jeffmhopkins/Open-Woodwind-Project/src/owp_synth/patches.ino

/*
 * The Open Woodwind Project - OWP_Synth for Woodwind Controllers by Jeff Hopkins
 * 
 * =============================================================================================================================================
 * 
 * Handles saving and loading the patch files from the SD card and EEPROM, defines the CC numbers
 * 
 */
 
#include <EEPROM.h>

#define CC_MODULATION_WHEEL               1
#define CC_BREATH                         2
#define CC_EXPRESSION                     11
#define CC_BREATH_TO_PULSE_WIDTH          20
#define CC_BREATH_TO_FILTER_CUTOFF        21
#define CC_BREATH_TO_FILTER_RESONANCE     22
#define CC_BREATH_TO_OVERDRIVE            23
#define CC_MODULATION_TO_PULSE_WIDTH      24
#define CC_MODULATION_TO_FILTER_CUTOFF    25
#define CC_MODULATION_TO_FILTER_RESONANCE 26
#define CC_MODULATION_TO_OVERDRIVE        27
#define CC_EXPRESSION_TO_PULSE_WIDTH      28
#define CC_EXPRESSION_TO_FILTER_CUTOFF    29
#define CC_EXPRESSION_TO_FILTER_RESONANCE 30
#define CC_EXPRESSION_TO_PORTAMENTO       31
#define CC_EXPRESSION_TO_OVERDRIVE        32
#define CC_PORTAMENTO_MIN_MULTIPLIER      33
#define CC_WAV_PLAYER                     34
#define CC_WAV_PLAYER_GAIN                35
#define CC_LOAD_PATCH                     36
#define CC_SAVE_PATCH                     37
#define CC_LFO1_FREQUENCY                 38
#define CC_LFO1_AMOUNT                    39
#define CC_LFO1_RANGE                     40
#define CC_WAVE1_SHAPE                    41
#define CC_WAVE2_SHAPE                    42
#define CC_WAVE3_SHAPE                    43
#define CC_WAVE4_SHAPE                    44
#define CC_LFO2_FREQUENCY                 45
#define CC_LFO2_AMOUNT                    46
#define CC_LFO2_RANGE                     47
#define CC_MODULATION_TO_LFO1_GAIN        48
#define CC_BREATH_TO_LFO1_GAIN            49
#define CC_EXPRESSION_TO_LFO1_GAIN        50
#define CC_WAVE1_GAIN                     51
#define CC_WAVE2_GAIN                     52
#define CC_WAVE3_GAIN                     53
#define CC_WAVE4_GAIN                     54
#define CC_MODULATION_TO_LFO1_FREQ        55
#define CC_BREATH_TO_LFO1_FREQ            56
#define CC_EXPRESSION_TO_LFO1_FREQ        57
#define CC_MODULATION_TO_LFO2_GAIN        58
#define CC_BREATH_TO_LFO2_GAIN            59
#define CC_EXPRESSION_TO_LFO2_GAIN        60
#define CC_WAVE1_DETUNE_MULTIPLIER        61
#define CC_WAVE2_DETUNE_MULTIPLIER        62
#define CC_WAVE3_DETUNE_MULTIPLIER        63
#define CC_WAVE4_DETUNE_MULTIPLIER        64
#define CC_MODULATION_TO_LFO2_FREQ        65
#define CC_BREATH_TO_LFO2_FREQ            66
#define CC_EXPRESSION_TO_LFO2_FREQ        67
#define CC_MODULATION_TO_LFO1_RANGE       68
#define CC_BREATH_TO_LFO1_RANGE           69
#define CC_EXPRESSION_TO_LFO1_RANGE       70
#define CC_WAVE1_PULSE_WIDTH              71
#define CC_WAVE2_PULSE_WIDTH              72
#define CC_WAVE3_PULSE_WIDTH              73
#define CC_WAVE4_PULSE_WIDTH              74
#define CC_FILTER_RESONANCE_OFFSET        76
#define CC_NOTE_OFFSET                    77
#define CC_FINE_TUNING                    78
#define CC_MASTER_VOLUME                  81
#define CC_FILTER_FREQUENCY_OFFSET        82
#define CC_NOISE_PINK_GAIN                83
#define CC_NOISE_WHITE_GAIN               84
#define CC_EFFECTS_MIXER_CLEAN            85
#define CC_EFFECTS_MIXER_FLANGE           86
#define CC_EFFECTS_MIXER_CHORUS           87
#define CC_EFFECTS_MIXER_DELAY            90
#define CC_REVERB_ROOM_SIZE               91
#define CC_EFFECTS_MIXER_DELAY_MS         92
#define CC_MODULATION_TO_LFO2_RANGE       93
#define CC_BREATH_TO_LFO2_RANGE           94
#define CC_EXPRESSION_TO_LFO2_RANGE       95
#define CC_WAVESHAPE1_GAIN                96
#define CC_WAVESHAPE2_GAIN                97
#define CC_WAVESHAPE3_GAIN                98
#define CC_WAVESHAPE4_GAIN                99
#define CC_WAVESHAPE_MODULATION_MULTIPLIER        100
#define CC_WAVESHAPE_MODULATION_MULTIPLIER_OFFSET 101
#define CC_WAVESHAPE_CLEAN_GAIN                   102
#define CC_LFO1_DESTINATION_FREQUENCY     103
#define CC_LFO1_DESTINATION_GAIN          104
#define CC_LFO1_DESTINATION_FILTER        105
#define CC_LFO2_DESTINATION_FREQUENCY     106
#define CC_LFO2_DESTINATION_GAIN          107
#define CC_LFO2_DESTINATION_FILTER        108
#define CC_LFO_RESET_PHASE_ON_NEW_NOTE    109
#define CC_BREATH_TO_WAVE2_WAVE3_WAVE4_GAIN     110
#define CC_MODULATION_TO_WAVE2_WAVE3_WAVE4_GAIN 111
#define CC_EXPRESSION_TO_WAVE2_WAVE3_WAVE4_GAIN 112
#define CC_WAVE2_WAVE3_WAVE4_GAIN_MODULATION_OFFSET   113 
#define CC_VCA_GATE_BYPASS                114
#define CC_FILTER_BYPASS                  115
#define CC_FILTER_TYPE                    116
#define CC_AUDIO_IN_PRE                   117
#define CC_AUDIO_IN_POST                  118
#define CC_EQ_1                           12
#define CC_EQ_2                           13
#define CC_EQ_3                           14
#define CC_EQ_4                           15
#define CC_EQ_5                           16
#define CC_BREATH_GAMMA                   17
#define CC_REVERB_WET                     18

struct Patch {
  float wave1_shape, wave2_shape, wave3_shape, wave4_shape;
  float wave1_pulse_width, wave2_pulse_width, wave3_pulse_width, wave4_pulse_width;
  float wave1_detune_multiplier, wave2_detune_multiplier, wave3_detune_multiplier, wave4_detune_multiplier;
  float wave1_gain,  wave2_gain,  wave3_gain,  wave4_gain;
  float master_volume, reverb_size;
  float noise_pink_gain, noise_white_gain;
  float filter_min_frequency, filter_q;
  float breath_to_pulse_width, breath_to_filter_cutoff, breath_to_filter_resonance, breath_to_overdrive;
  float modulation_to_pulse_width, modulation_to_filter_cutoff, modulation_to_filter_resonance, modulation_to_overdrive;
  float expression_to_pulse_width, expression_to_filter_cutoff, expression_to_filter_resonance, expression_to_portamento, expression_to_overdrive;
  float note_offset, default_tune;
  float effects_oscillators, effects_flange, effects_chorus, effects_delay, effects_delay_ms;
  float portamento_min_multiplier;
  float wav_gain;
  float lfo1_gain, lfo1_freq, lfo1_range;
  float breath_to_lfo1_gain, modulation_to_lfo1_gain, expression_to_lfo1_gain;
  float breath_to_lfo1_freq, modulation_to_lfo1_freq, expression_to_lfo1_freq;
  float lfo2_gain, lfo2_freq, lfo2_range;
  float breath_to_lfo2_gain, modulation_to_lfo2_gain, expression_to_lfo2_gain;
  float breath_to_lfo2_freq, modulation_to_lfo2_freq, expression_to_lfo2_freq;
  float waveshape1_gain, waveshape2_gain, waveshape3_gain, waveshape4_gain;
  float waveshape_modulation_multiplier, waveshape_modulation_multiplier_offset;
  float waveshape_clean_gain;
  float lfo1_destination_frequency, lfo1_destination_gain, lfo1_destination_filter;
  float lfo2_destination_frequency, lfo2_destination_gain, lfo2_destination_filter;
  float lfo_reset_phase_on_new_note;
  float breath_to_wave2_wave3_wave4_gain, modulation_to_wave2_wave3_wave4_gain, expression_to_wave2_wave3_wave4_gain;
  float wave2_wave3_wave4_gain_modulation_offset;
  float vca_gate_bypass, filter_bypass, filter_type; 
  float audio_in_pre, audio_in_post;
  float eq_1, eq_2, eq_3, eq_4, eq_5;
  float breath_gamma;
  float reverb_wet;
};

Patch eeprom_patch;       //This patch is loaded from eeprom
Patch loadedPatches[127]; //These patches are loaded from SD card into this array, this takes like 25% of the dynamic memory of the Teensy 4.0
bool  patchLoaded[127];   //Defines clean/dirty patch slots from what we've loaded from SD

File  dataFile;

void configureSD() {
  SPI.setMOSI(11); SPI.setSCK(13);
  if (!(SD.begin(10))) {
      Serial.println("Unable to access the SD card");
      loadPatchEEPROM();
  }
  for(int i=0;i < 127;i++) {
    if(SD.exists(String(String(i, DEC) +".PAT").c_str())) {
      dataFile = SD.open(String(String(i, DEC) +".PAT").c_str());
      dataFile.read(&loadedPatches[i], sizeof(Patch));
      dataFile.close();
      patchLoaded[i] = true;
    } else {
      patchLoaded[i] = false;
    }
  }
}

void savePatchSD(int i) {
  loadedPatches[i] = createPatch();
  patchLoaded[i] = true;
  if (SD.exists(String(String(i, DEC) +".PAT").c_str())) {
    SD.remove(String(String(i, DEC) +".PAT").c_str());
  }
  dataFile = SD.open(String(String(i, DEC) +".PAT").c_str(), FILE_WRITE);
  if(!dataFile) {
    Serial.println("Could not create file");
    wavplayer.play("err.wav");
  } else {
    Serial.print("size: ");
    Serial.print(sizeof(Patch));
    Serial.println();
    dataFile.write((byte*)&loadedPatches[i], sizeof(Patch));
    Serial.write((byte*)&loadedPatches[i], sizeof(Patch));
    dataFile.close();
  }
}

void loadPatchSD(int i) {
  if(patchLoaded[i]) {
    initialize_patch(loadedPatches[i]);
  } else {
    dataFile = SD.open(String(String(i, DEC) +".PAT").c_str());
    if(!dataFile) {
      Serial.println("Could not load file");
      wavplayer.play("err.wav");
    } else {
      int bytes = dataFile.read(&loadedPatches[i], sizeof(Patch));
      dataFile.close();
      Serial.print("Loaded:");Serial.println(bytes, DEC);
      patchLoaded[i] = true;
      initialize_patch(loadedPatches[i]);
    }
  }
}

void savePatchEEPROM() {
  EEPROM.put(0, createPatch());  
}

void loadPatchEEPROM() {
  EEPROM.get(0, eeprom_patch);
  initialize_patch(eeprom_patch);
}

struct Patch createPatch() {
  Patch temp_patch = {wave1_shape, wave2_shape, wave3_shape, wave4_shape,
                  wave1_pulse_width, wave2_pulse_width, wave3_pulse_width, wave4_pulse_width,
                  wave1_detune_multiplier,wave2_detune_multiplier,wave3_detune_multiplier,wave4_detune_multiplier,
                  wave1_gain,  wave2_gain,  wave3_gain,  wave4_gain,
                  master_volume, reverb_size,
                  noise_pink_gain, noise_white_gain,
                  filter_min_frequency, filter_q,
                  breath_to_pulse_width, breath_to_filter_cutoff, breath_to_filter_resonance, breath_to_overdrive,
                  modulation_to_pulse_width, modulation_to_filter_cutoff, modulation_to_filter_resonance, modulation_to_overdrive,
                  expression_to_pulse_width, expression_to_filter_cutoff, expression_to_filter_resonance, expression_to_portamento, expression_to_overdrive,
                  note_offset, default_tune,
                  effects_oscillators, effects_flange, effects_chorus, effects_delay, effects_delay_ms,
                  portamento_min_multiplier,
                  wav_gain,
                  lfo1_gain, lfo1_freq, lfo1_range,
                  breath_to_lfo1_gain, modulation_to_lfo1_gain, expression_to_lfo1_gain,
                  breath_to_lfo1_freq, modulation_to_lfo1_freq, expression_to_lfo1_freq,
                  lfo2_gain, lfo2_freq, lfo2_range,
                  breath_to_lfo2_gain, modulation_to_lfo2_gain, expression_to_lfo2_gain,
                  breath_to_lfo2_freq, modulation_to_lfo2_freq, expression_to_lfo2_freq,
                  waveshape1_gain, waveshape2_gain, waveshape3_gain, waveshape4_gain,
                  waveshape_modulation_multiplier, waveshape_modulation_multiplier_offset,
                  waveshape_clean_gain,
                  lfo1_destination_frequency, lfo1_destination_gain, lfo1_destination_filter,
                  lfo2_destination_frequency, lfo2_destination_gain, lfo1_destination_filter,
                  lfo_reset_phase_on_new_note,
                  breath_to_wave2_wave3_wave4_gain, modulation_to_wave2_wave3_wave4_gain, expression_to_wave2_wave3_wave4_gain,
                  wave2_wave3_wave4_gain_modulation_offset,
                  vca_gate_bypass,filter_bypass,filter_type,
                  audio_in_pre, audio_in_post,
                  eq_1, eq_2, eq_3, eq_4, eq_5,
                  breath_gamma,
                  reverb_wet};
  return temp_patch;
}

void initialize_patch(struct Patch patch) {
    wave1.begin(patch.wave1_shape); 
    wave2.begin(patch.wave2_shape);
    wave3.begin(patch.wave3_shape);
    wave4.begin(patch.wave4_shape);
    wave1_pulse_width = patch.wave1_pulse_width;
    wave2_pulse_width = patch.wave2_pulse_width;
    wave3_pulse_width = patch.wave3_pulse_width;
    wave4_pulse_width = patch.wave4_pulse_width;
    wave1_detune_multiplier = patch.wave1_detune_multiplier;
    wave2_detune_multiplier = patch.wave2_detune_multiplier;
    wave3_detune_multiplier = patch.wave3_detune_multiplier;
    wave4_detune_multiplier = patch.wave4_detune_multiplier;
    waveselect.gain(0, patch.wave1_gain); wave1_gain = patch.wave1_gain;
    waveselect.gain(1, patch.wave2_gain); wave2_gain = patch.wave2_gain;
    waveselect.gain(2, patch.wave3_gain); wave3_gain = patch.wave3_gain;
    waveselect.gain(3, patch.wave4_gain); wave4_gain = patch.wave4_gain;
    master_volume = patch.master_volume;
    reverb_size   = patch.reverb_size;
    noise_pink_gain = patch.noise_pink_gain;
    noise_white_gain = patch.noise_white_gain;
    filter_min_frequency = patch.filter_min_frequency;
    filter_q = patch.filter_q;
    breath_to_pulse_width  = patch.breath_to_pulse_width;
    breath_to_filter_cutoff = patch.breath_to_filter_cutoff;
    breath_to_filter_resonance = patch.breath_to_filter_resonance;
    breath_to_overdrive = patch.breath_to_overdrive;
    modulation_to_pulse_width = patch.modulation_to_pulse_width;
    modulation_to_filter_cutoff = patch.modulation_to_filter_cutoff;
    modulation_to_filter_resonance = patch.modulation_to_filter_resonance;
    modulation_to_overdrive = patch.modulation_to_overdrive;
    expression_to_pulse_width = patch.expression_to_pulse_width;
    expression_to_filter_cutoff = patch.expression_to_filter_cutoff;
    expression_to_filter_resonance = patch.expression_to_filter_resonance;
    expression_to_portamento = patch.expression_to_portamento;
    expression_to_overdrive = patch.expression_to_overdrive;
    note_offset = patch.note_offset;
    default_tune = patch.default_tune;
    effects_oscillators = patch.effects_oscillators;
    effects_flange = patch.effects_flange;
    effects_chorus = patch.effects_chorus;
    effects_delay = patch.effects_delay;
    effects_delay_ms = patch.effects_delay_ms;
    portamento_min_multiplier = patch.portamento_min_multiplier;
    wav_gain = patch.wav_gain;
    lfo1_gain = patch.lfo1_gain;
    lfo1_freq = patch.lfo1_freq;
    lfo1_range = patch.lfo1_range;
    breath_to_lfo1_gain = patch.breath_to_lfo1_gain;
    modulation_to_lfo1_gain = patch.modulation_to_lfo1_gain;
    expression_to_lfo1_gain = patch.expression_to_lfo1_gain;
    breath_to_lfo1_freq = patch.breath_to_lfo1_freq;
    modulation_to_lfo1_freq = patch.modulation_to_lfo1_freq;
    expression_to_lfo1_freq = patch.expression_to_lfo1_freq;
    lfo2_gain = patch.lfo2_gain;
    lfo2_freq = patch.lfo2_freq;
    lfo2_range = patch.lfo2_range;
    breath_to_lfo2_gain = patch.breath_to_lfo2_gain;
    modulation_to_lfo2_gain = patch.modulation_to_lfo2_gain;
    expression_to_lfo2_gain = patch.expression_to_lfo2_gain;
    breath_to_lfo2_freq = patch.breath_to_lfo2_freq;
    modulation_to_lfo2_freq = patch.modulation_to_lfo2_freq;
    expression_to_lfo2_freq = patch.expression_to_lfo2_freq;
    waveshape1_gain = patch.waveshape1_gain;
    waveshape2_gain = patch.waveshape2_gain;
    waveshape3_gain = patch.waveshape3_gain;
    waveshape4_gain = patch.waveshape4_gain;
    waveshape_modulation_multiplier = patch.waveshape_modulation_multiplier;
    waveshape_modulation_multiplier_offset = patch.waveshape_modulation_multiplier_offset;
    waveshape_clean_gain = patch.waveshape_clean_gain;
    lfo1_destination_frequency = patch.lfo1_destination_frequency;
    lfo1_destination_gain = patch.lfo1_destination_gain;
    lfo1_destination_filter = patch.lfo1_destination_filter;
    lfo2_destination_frequency = patch.lfo2_destination_frequency;
    lfo2_destination_gain = patch.lfo2_destination_gain;
    lfo1_destination_filter = patch.lfo1_destination_filter;
    lfo_reset_phase_on_new_note = patch.lfo_reset_phase_on_new_note;
    breath_to_wave2_wave3_wave4_gain = patch.breath_to_wave2_wave3_wave4_gain;
    modulation_to_wave2_wave3_wave4_gain = patch.modulation_to_wave2_wave3_wave4_gain;
    expression_to_wave2_wave3_wave4_gain = patch.expression_to_wave2_wave3_wave4_gain;
    wave2_wave3_wave4_gain_modulation_offset = patch.wave2_wave3_wave4_gain_modulation_offset;
    vca_gate_bypass = patch.vca_gate_bypass;
    filter_bypass = patch.filter_bypass;
    filter_type = patch.filter_type;
    audio_in_pre = patch.audio_in_pre;
    audio_in_post = patch.audio_in_post;
    eq_1 = patch.eq_1;
    eq_2 = patch.eq_2;
    eq_3 = patch.eq_3;
    eq_4 = patch.eq_4;
    eq_5 = patch.eq_5;
    sgtl5000_1.eqBands(eq_1, eq_2, eq_3, eq_4, eq_5);
    breath_gamma = patch.breath_gamma;
    reverb_wet = patch.reverb_wet;
    updateOSC();
}

void updateOSC() {
  sendcc(CC_WAVE1_SHAPE, wave1_shape);
  sendcc(CC_WAVE2_SHAPE, wave2_shape);
  sendcc(CC_WAVE3_SHAPE, wave3_shape);
  sendcc(CC_WAVE4_SHAPE, wave4_shape);
  sendcc(CC_WAVE1_PULSE_WIDTH, wave1_pulse_width);
  sendcc(CC_WAVE2_PULSE_WIDTH, wave2_pulse_width);
  sendcc(CC_WAVE3_PULSE_WIDTH, wave3_pulse_width);
  sendcc(CC_WAVE4_PULSE_WIDTH, wave4_pulse_width);
  sendcc(CC_WAVE1_DETUNE_MULTIPLIER, wave1_detune_multiplier);
  sendcc(CC_WAVE2_DETUNE_MULTIPLIER, wave2_detune_multiplier);
  sendcc(CC_WAVE3_DETUNE_MULTIPLIER, wave3_detune_multiplier);
  sendcc(CC_WAVE4_DETUNE_MULTIPLIER, wave4_detune_multiplier);
  sendcc(CC_WAVE1_GAIN, wave1_gain);
  sendcc(CC_WAVE2_GAIN, wave2_gain);
  sendcc(CC_WAVE3_GAIN, wave3_gain);
  sendcc(CC_WAVE4_GAIN, wave4_gain);
  sendcc(CC_MASTER_VOLUME, master_volume);
  sendcc(CC_REVERB_ROOM_SIZE, reverb_size);
  sendcc(CC_NOISE_PINK_GAIN, noise_pink_gain);
  sendcc(CC_NOISE_WHITE_GAIN, noise_white_gain);
  sendcc(CC_FILTER_FREQUENCY_OFFSET, filter_min_frequency);
  sendcc(CC_FILTER_RESONANCE_OFFSET, filter_q);
  sendcc(CC_BREATH_TO_PULSE_WIDTH, breath_to_pulse_width);
  sendcc(CC_BREATH_TO_FILTER_CUTOFF, breath_to_filter_cutoff);
  sendcc(CC_BREATH_TO_FILTER_RESONANCE, breath_to_filter_resonance);
  sendcc(CC_BREATH_TO_OVERDRIVE, breath_to_overdrive);
  sendcc(CC_MODULATION_TO_PULSE_WIDTH, modulation_to_pulse_width);
  sendcc(CC_MODULATION_TO_FILTER_CUTOFF, modulation_to_filter_cutoff);
  sendcc(CC_MODULATION_TO_FILTER_RESONANCE, modulation_to_filter_resonance);
  sendcc(CC_MODULATION_TO_OVERDRIVE, modulation_to_overdrive);
  sendcc(CC_EXPRESSION_TO_PULSE_WIDTH, expression_to_pulse_width);
  sendcc(CC_EXPRESSION_TO_FILTER_CUTOFF, expression_to_filter_cutoff);
  sendcc(CC_EXPRESSION_TO_FILTER_RESONANCE, expression_to_filter_resonance);
  sendcc(CC_EXPRESSION_TO_PORTAMENTO, expression_to_portamento);
  sendcc(CC_EXPRESSION_TO_OVERDRIVE, expression_to_overdrive);
  sendcc(CC_NOTE_OFFSET, note_offset/127.0);
  sendcc(CC_EFFECTS_MIXER_CLEAN, effects_oscillators);
  sendcc(CC_EFFECTS_MIXER_FLANGE, effects_flange);
  sendcc(CC_EFFECTS_MIXER_CHORUS, effects_chorus);
  sendcc(CC_EFFECTS_MIXER_DELAY, effects_delay);
  sendcc(CC_EFFECTS_MIXER_DELAY_MS, effects_delay_ms);
  sendcc(CC_PORTAMENTO_MIN_MULTIPLIER, portamento_min_multiplier);
  sendcc(CC_WAV_PLAYER_GAIN, wav_gain);
  sendcc(CC_LFO1_AMOUNT, lfo1_gain);
  sendcc(CC_LFO1_FREQUENCY, lfo1_freq);
  sendcc(CC_LFO1_RANGE, lfo1_range);
  sendcc(CC_BREATH_TO_LFO1_GAIN, breath_to_lfo1_gain);
  sendcc(CC_MODULATION_TO_LFO1_GAIN, modulation_to_lfo1_gain);
  sendcc(CC_EXPRESSION_TO_LFO1_GAIN, expression_to_lfo1_gain);
  sendcc(CC_BREATH_TO_LFO1_FREQ, breath_to_lfo1_freq);
  sendcc(CC_MODULATION_TO_LFO1_FREQ, modulation_to_lfo1_freq);
  sendcc(CC_EXPRESSION_TO_LFO1_FREQ, expression_to_lfo1_freq);
  sendcc(CC_LFO2_AMOUNT, lfo2_gain);
  sendcc(CC_LFO2_FREQUENCY, lfo2_freq);
  sendcc(CC_LFO2_RANGE, lfo2_range);
  sendcc(CC_BREATH_TO_LFO2_GAIN, breath_to_lfo2_gain);
  sendcc(CC_MODULATION_TO_LFO2_GAIN, modulation_to_lfo2_gain);
  sendcc(CC_EXPRESSION_TO_LFO2_GAIN, expression_to_lfo2_gain);
  sendcc(CC_BREATH_TO_LFO2_FREQ, breath_to_lfo2_freq);
  sendcc(CC_MODULATION_TO_LFO2_FREQ, modulation_to_lfo2_freq);
  sendcc(CC_EXPRESSION_TO_LFO2_FREQ, expression_to_lfo2_freq);
  sendcc(CC_WAVESHAPE1_GAIN, waveshape1_gain);
  sendcc(CC_WAVESHAPE2_GAIN, waveshape2_gain);
  sendcc(CC_WAVESHAPE3_GAIN, waveshape3_gain);
  sendcc(CC_WAVESHAPE4_GAIN, waveshape4_gain);
  sendcc(CC_WAVESHAPE_MODULATION_MULTIPLIER, waveshape_modulation_multiplier);
  sendcc(CC_WAVESHAPE_MODULATION_MULTIPLIER_OFFSET, waveshape_modulation_multiplier_offset);
  sendcc(CC_WAVESHAPE_CLEAN_GAIN, waveshape_clean_gain);
  sendcc(CC_LFO1_DESTINATION_FREQUENCY, lfo1_destination_frequency);
  sendcc(CC_LFO1_DESTINATION_GAIN, lfo1_destination_gain);
  sendcc(CC_LFO1_DESTINATION_FILTER, lfo1_destination_filter);
  sendcc(CC_LFO2_DESTINATION_FREQUENCY, lfo2_destination_frequency);
  sendcc(CC_LFO2_DESTINATION_GAIN, lfo2_destination_gain);
  sendcc(CC_LFO2_DESTINATION_FILTER, lfo2_destination_filter);
  sendcc(CC_LFO_RESET_PHASE_ON_NEW_NOTE, lfo_reset_phase_on_new_note);
  sendcc(CC_BREATH_TO_WAVE2_WAVE3_WAVE4_GAIN, breath_to_wave2_wave3_wave4_gain);
  sendcc(CC_MODULATION_TO_WAVE2_WAVE3_WAVE4_GAIN, modulation_to_wave2_wave3_wave4_gain); 
  sendcc(CC_EXPRESSION_TO_WAVE2_WAVE3_WAVE4_GAIN, expression_to_wave2_wave3_wave4_gain);
  sendcc(CC_WAVE2_WAVE3_WAVE4_GAIN_MODULATION_OFFSET, wave2_wave3_wave4_gain_modulation_offset);
  sendcc(CC_VCA_GATE_BYPASS, vca_gate_bypass);
  sendcc(CC_FILTER_BYPASS, filter_bypass);
  sendcc(CC_FILTER_TYPE, filter_type);
  sendcc(CC_AUDIO_IN_PRE, audio_in_pre);
  sendcc(CC_AUDIO_IN_POST, audio_in_post);
  sendcc(CC_EQ_1, (eq_1+1.0)/2.0);
  sendcc(CC_EQ_2, (eq_2+1.0)/2.0);
  sendcc(CC_EQ_3, (eq_3+1.0)/2.0);
  sendcc(CC_EQ_4, (eq_4+1.0)/2.0);
  sendcc(CC_EQ_5, (eq_5+1.0)/2.0);
  sendcc(CC_BREATH_GAMMA, 3.0*breath_gamma);
  sendcc(CC_REVERB_WET, reverb_wet);
}

void sendcc(int cc, float value) {
  usbMIDI.sendControlChange(cc, (int)(value*127.0), 0);
}
